SamEberl/MicroMouse/Firmware/include/general.h

/* Microchip Technology Inc. and its subsidiaries.  You may use this software 
 * and any derivatives exclusively with Microchip products. 
 * 
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
 * IN NO EVENT WILL MICROCHIP BE LIABLE FOR ANY INDIRECT, SPECIAL, PUNITIVE, 
 * INCIDENTAL OR CONSEQUENTIAL LOSS, DAMAGE, COST OR EXPENSE OF ANY KIND 
 * WHATSOEVER RELATED TO THE SOFTWARE, HOWEVER CAUSED, EVEN IF MICROCHIP HAS 
 * BEEN ADVISED OF THE POSSIBILITY OR THE DAMAGES ARE FORESEEABLE.  TO THE 
 * FULLEST EXTENT ALLOWED BY LAW, MICROCHIP'S TOTAL LIABILITY ON ALL CLAIMS 
 * IN ANY WAY RELATED TO THIS SOFTWARE WILL NOT EXCEED THE AMOUNT OF FEES, IF 
 * ANY, THAT YOU HAVE PAID DIRECTLY TO MICROCHIP FOR THIS SOFTWARE.
 *
 * MICROCHIP PROVIDES THIS SOFTWARE CONDITIONALLY UPON YOUR ACCEPTANCE OF THESE 
 * TERMS. 
 */

/* 
 * File:   
 * Author: 
 * Comments:
 * Revision history: 
 */

// This is a guard condition so that contents of this file are not included
// more than once.  
#ifndef __GENERAL_H__
#define	__GENERAL_H__

#define TCYCLE_MS 0.0000375
#define TRUE 1
#define FALSE 0

//Global Types

typedef enum errorCode{
    OK,
    GENERAL_ERROR,
    INVALID_ARGUMENT_ERROR,
    OUT_OF_BOUNDS_ERROR,
    UNINITIALIZED,
    BUSY
}errorCode;

typedef enum LEDState{
    ON,
    OFF
}LEDstate;
//Functions

errorCode sendPotiValue(unsigned char potiVal);
#endif	/* __GENERAL_H__ */
