SamEberl/MicroMouse/Simulation/src/draw.cpp

#include <SDL2/SDL.h>
#include <cmath>
#include <iostream>
#include "draw.h"
#include "classes.h"
#include "defs.h"
#include "estimations.h"

using namespace std;

void drawSquareGrid(SDL_Renderer *renderer, int sideLength)
{
    // Set the color for the grid cell
    SDL_SetRenderDrawColor(renderer, 0, 0, 0, 255);
    for (int i = 0; i <= sideLength; i += 1)
    {
        SDL_RenderDrawLine(renderer, 0, i*CELL_SIZE, sideLength*CELL_SIZE, i*CELL_SIZE);
        SDL_RenderDrawLine(renderer, i*CELL_SIZE, 0, i*CELL_SIZE, sideLength*CELL_SIZE);
    }
}

void drawCircle(SDL_Renderer *renderer, int x, int y, int radius) {
    for (int i = 0; i < 360; i++) {
        float degInRad = i * M_PI / 180;
        for (int j = radius; j > 0; j--) {
            SDL_RenderDrawPoint(renderer, x + cos(degInRad) * j, y + sin(degInRad) * j);
        }
    }
}

void drawSquare(SDL_Renderer *renderer, int x, int y, int w, int h)
{
  SDL_Rect rect = {x, y, w, h};
  SDL_RenderFillRect(renderer, &rect);
}

void drawRotatedSquare(SDL_Renderer *renderer, float x, float y, float direction_x, float direction_y, float width, float height) {
    float alpha = atan2(direction_y, direction_x);
    float ca = cos(alpha);
    float sa = sin(alpha);
    int x1, y1, x2, y2, x3, y3, x4, y4;
    x1 = ca*(width/2) + -sa*(height/2) + x;
    y1 = sa*(width/2) + ca*(height/2) + y;
    x2 = ca*(width/2) + -sa*(-height/2) + x;
    y2 = sa*(width/2) + ca*(-height/2) + y;
    x3 = ca*(-width/2) + -sa*(-height/2) + x;
    y3 = sa*(-width/2) + ca*(-height/2) + y;
    x4 = ca*(-width/2) + -sa*(height/2) + x;
    y4 = sa*(-width/2) + ca*(height/2) + y;
    SDL_RenderDrawLine(renderer, x1, y1, x2, y2);
    SDL_RenderDrawLine(renderer, x2, y2, x3, y3);
    SDL_RenderDrawLine(renderer, x3, y3, x4, y4);
    SDL_RenderDrawLine(renderer, x4, y4, x1, y1);
}


void drawRobo(SDL_Renderer *renderer, Robot mouse){
    float x = mouse.rob_pos[0];
    float y = mouse.rob_pos[1];
    float x_dir = cos(mouse.rob_dir);
    float y_dir = sin(mouse.rob_dir);
    float width = mouse.width;
    float height = mouse.height;
    SDL_SetRenderDrawColor(renderer, 0, 200, 0, SDL_ALPHA_OPAQUE);
    drawRotatedSquare(renderer, x, y, x_dir, y_dir, height, width);
    SDL_SetRenderDrawColor(renderer, 0, 200, 0, SDL_ALPHA_OPAQUE);
    SDL_RenderDrawLine(renderer, x, y, x+x_dir*height/2, y+y_dir*height/2);

    drawSensor(renderer, mouse.sensR);
    drawSensor(renderer, mouse.sensR2);
    drawSensor(renderer, mouse.sensS);
    drawSensor(renderer, mouse.sensL2);
    drawSensor(renderer, mouse.sensL);

    float start_x;
    float start_y;
    float end_x = mouse.taken_path[0][0];
    float end_y = mouse.taken_path[0][1];

    for (int i = 0; i < mouse.taken_path.size(); i += 1){
        start_x = end_x;
        start_y = end_y;

        end_x = mouse.taken_path[i][0];
        end_y = mouse.taken_path[i][1];

        SDL_SetRenderDrawColor(renderer, 0, 200, 0, SDL_ALPHA_OPAQUE);
        SDL_RenderDrawLine(renderer, start_x, start_y, end_x, end_y);
    }
}

void drawRobo(SDL_Renderer *renderer, RobotEst mouse){
    float x = mouse.rob_pos[0];
    float y = mouse.rob_pos[1];
    float x_dir = cos(mouse.rob_dir);
    float y_dir = sin(mouse.rob_dir);
    float width = mouse.width;
    float height = mouse.height;
    SDL_SetRenderDrawColor(renderer, 0, 0, 0, SDL_ALPHA_OPAQUE);
    drawRotatedSquare(renderer, x, y, x_dir, y_dir, height, width);
    SDL_SetRenderDrawColor(renderer, 0, 0, 0, SDL_ALPHA_OPAQUE);
    SDL_RenderDrawLine(renderer, x, y, x+x_dir*height/2, y+y_dir*height/2);

    drawSensor(renderer, mouse.sensR);
    drawSensor(renderer, mouse.sensR2);
    drawSensor(renderer, mouse.sensS);
    drawSensor(renderer, mouse.sensL2);
    drawSensor(renderer, mouse.sensL);
}

void drawSensor(SDL_Renderer *renderer, Sensor sensor){
    float x = sensor.sens_pos[0];
    float y = sensor.sens_pos[1];
    SDL_SetRenderDrawColor(renderer, 0, 255, 0, SDL_ALPHA_OPAQUE);
    SDL_RenderDrawLine(renderer, x, y,
                        x + cos(sensor.sens_dir)*sensor.dist_measure, 
                        y + sin(sensor.sens_dir)*sensor.dist_measure);
}

void drawSensor(SDL_Renderer *renderer, SensorEst sensor){
    float x = sensor.sens_pos[0];
    float y = sensor.sens_pos[1];
    SDL_SetRenderDrawColor(renderer, 0, 0, 0, SDL_ALPHA_OPAQUE);
    SDL_RenderDrawLine(renderer, x, y,
                        x + cos(sensor.sens_dir)*sensor.dist_measure, 
                        y + sin(sensor.sens_dir)*sensor.dist_measure);
}

void drawLabyrinth(SDL_Renderer *renderer, Cell labyrinth[LABYRINTH_WIDTH][LABYRINTH_HEIGHT], Corner corners[LABYRINTH_WIDTH+1][LABYRINTH_HEIGHT+1]){
    vector<float> p1(2), p2(2), p3(2), p4(2);

    for (int i = 0; i < LABYRINTH_WIDTH; i += 1){
        for (int j = 0; j < LABYRINTH_HEIGHT; j += 1){
            p1 = labyrinth[i][j].get_point('1');
            p2 = labyrinth[i][j].get_point('2');
            p3 = labyrinth[i][j].get_point('3');
            p4 = labyrinth[i][j].get_point('4');

            //draw north
            if (labyrinth[i][j].has_wall('N')){
                SDL_SetRenderDrawColor(renderer, 150, 150, 255, 255);
                SDL_RenderDrawLine(renderer, p1[0], p1[1], p2[0], p2[1]);
            }
            
            //draw east
            if (labyrinth[i][j].has_wall('E')){
                SDL_SetRenderDrawColor(renderer, 150, 150, 255, 255);
                SDL_RenderDrawLine(renderer, p2[0], p2[1], p3[0], p3[1]);
            }
            
            //draw south
            if (labyrinth[i][j].has_wall('S')){
                SDL_SetRenderDrawColor(renderer, 150, 150, 255, 255);
                SDL_RenderDrawLine(renderer, p4[0], p4[1], p3[0], p3[1]);
            }
            
            //draw west
            if (labyrinth[i][j].has_wall('W')){
                SDL_SetRenderDrawColor(renderer, 150, 150, 255, 255);
                SDL_RenderDrawLine(renderer, p1[0], p1[1], p4[0], p4[1]);
            }
        }
    }
    // Draw the corners
    for (int i = 0; i < LABYRINTH_WIDTH+1; i += 1){
        for (int j = 0; j < LABYRINTH_HEIGHT+1; j += 1){
            p1 = corners[i][j].get_point('1');
            p2 = corners[i][j].get_point('2');
            p3 = corners[i][j].get_point('3');
            p4 = corners[i][j].get_point('4');
            SDL_SetRenderDrawColor(renderer, 0, 0, 0, 128);
            SDL_RenderDrawLine(renderer, p1[0], p1[1], p2[0], p2[1]);
            SDL_RenderDrawLine(renderer, p2[0], p2[1], p3[0], p3[1]);
            SDL_RenderDrawLine(renderer, p4[0], p4[1], p3[0], p3[1]);
            SDL_RenderDrawLine(renderer, p1[0], p1[1], p4[0], p4[1]);
        }
    }
}

void drawLabyrinth(SDL_Renderer *renderer, CellEst labyrinth[LABYRINTH_WIDTH][LABYRINTH_HEIGHT]){
    vector<float> p1(2), p2(2), p3(2), p4(2);

    for (int i = 0; i < LABYRINTH_WIDTH; i += 1)
    {
        for (int j = 0; j < LABYRINTH_HEIGHT; j += 1){
            p1 = labyrinth[i][j].get_point('1');
            p2 = labyrinth[i][j].get_point('2');
            p3 = labyrinth[i][j].get_point('3');
            p4 = labyrinth[i][j].get_point('4');

            //draw north
            if (labyrinth[i][j].has_wall('N')){
                SDL_SetRenderDrawColor(renderer, 0, 0, 0, 128);
                SDL_RenderDrawLine(renderer, p1[0], p1[1], p2[0], p2[1]);
            }
            
            //draw east
            if (labyrinth[i][j].has_wall('E')){
                SDL_SetRenderDrawColor(renderer, 0, 0, 0, 128);
                SDL_RenderDrawLine(renderer, p2[0], p2[1], p3[0], p3[1]);
            }
            
            //draw south
            if (labyrinth[i][j].has_wall('S')){
                SDL_SetRenderDrawColor(renderer, 0, 0, 0, 128);
                SDL_RenderDrawLine(renderer, p4[0], p4[1], p3[0], p3[1]);
            }
            
            //draw west
            if (labyrinth[i][j].has_wall('W')){
                SDL_SetRenderDrawColor(renderer, 0, 0, 0, 128);
                SDL_RenderDrawLine(renderer, p1[0], p1[1], p4[0], p4[1]);
            }
        }
    }
}
