SamEberl/MicroMouse/Simulation/include/utils.h

#include <vector>
#include <stack>
#include "classes.h"
#include "estimations.h"

#ifndef UTILS_H
#define UTILS_H

using namespace std;

float distBetweenPoints(vector<float> p1, vector<float> p2);
int random_int(int min, int max);
float gaussianNoise(float mean, float stddev);
void init_labyrinth(Cell labyrinth[LABYRINTH_WIDTH][LABYRINTH_HEIGHT]);
void init_labyrinth(CellEst labyrinth[LABYRINTH_WIDTH][LABYRINTH_HEIGHT]);
void init_corners(Corner corners[LABYRINTH_WIDTH+1][LABYRINTH_HEIGHT+1]);
void init_corners(CornerEst corners[LABYRINTH_WIDTH+1][LABYRINTH_HEIGHT+1]) ;
void generate_labyrinth(Cell labyrinth[LABYRINTH_WIDTH][LABYRINTH_HEIGHT], Corner corners[LABYRINTH_WIDTH+1][LABYRINTH_HEIGHT+1]);
void generate_custom_labyrinth(Cell labyrinth[LABYRINTH_WIDTH][LABYRINTH_HEIGHT], Corner corners[LABYRINTH_WIDTH+1][LABYRINTH_HEIGHT+1]);
int print_labyrinth(Cell labyrinth[LABYRINTH_WIDTH][LABYRINTH_HEIGHT]);
vector<float> findIntersection(vector<float> starting_point, 
                                vector<float> end_point, 
                                vector<float> wall_point1, 
                                vector<float> wall_point2,
                                float& distance_to_intersection, 
                                bool& intersection_found);
vector<int> getCellFromPos(vector<float> rob_pos);


#endif
